photonZfeed/multiDradiometry/CAD/ND-Radiometry-Scanner/leadscrew_support_cap.stl

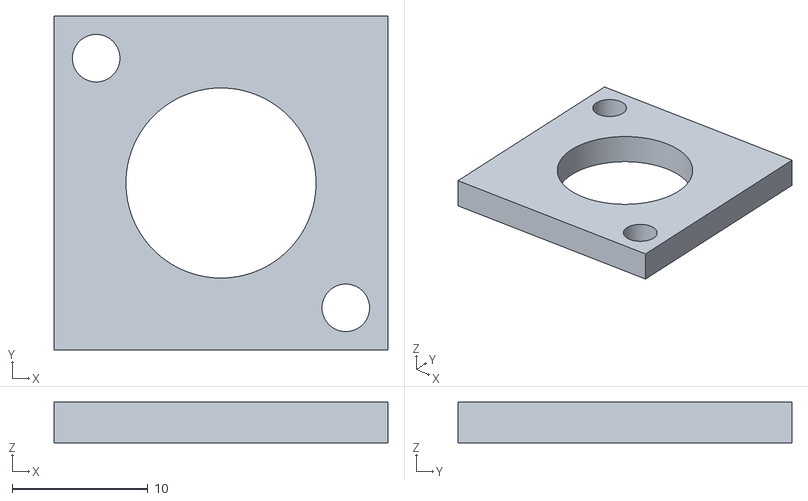
[picture p23: CAD file, 2021-06-03]
CAD/ND-Radiometry-Scanner/leadscrew_support_cap.stl
24.6 x 24.6 x 3.00
