photonZfeed/multiDradiometry/CAD/ND-Radiometry-Scanner/z-sled_nut_cover.stl

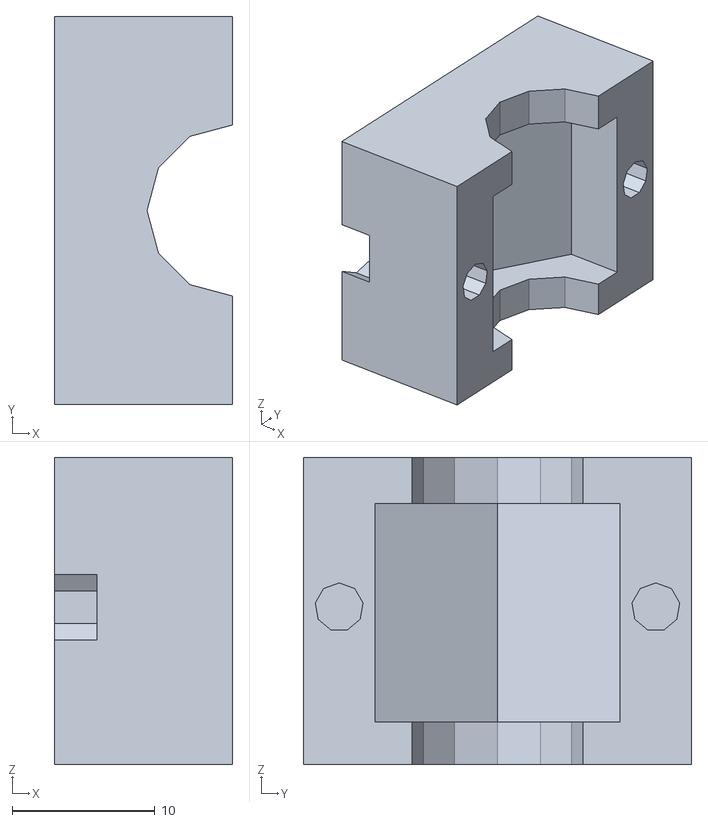
[picture p24: CAD file, 2021-06-03]
CAD/ND-Radiometry-Scanner/z-sled_nut_cover.stl
12.5 x 27.2 x 21.5
