photonZfeed/multiDradiometry/Python/ITOM_script/02Results/210430_115323_example_name/11.58_mm/Colormapexample_name.png

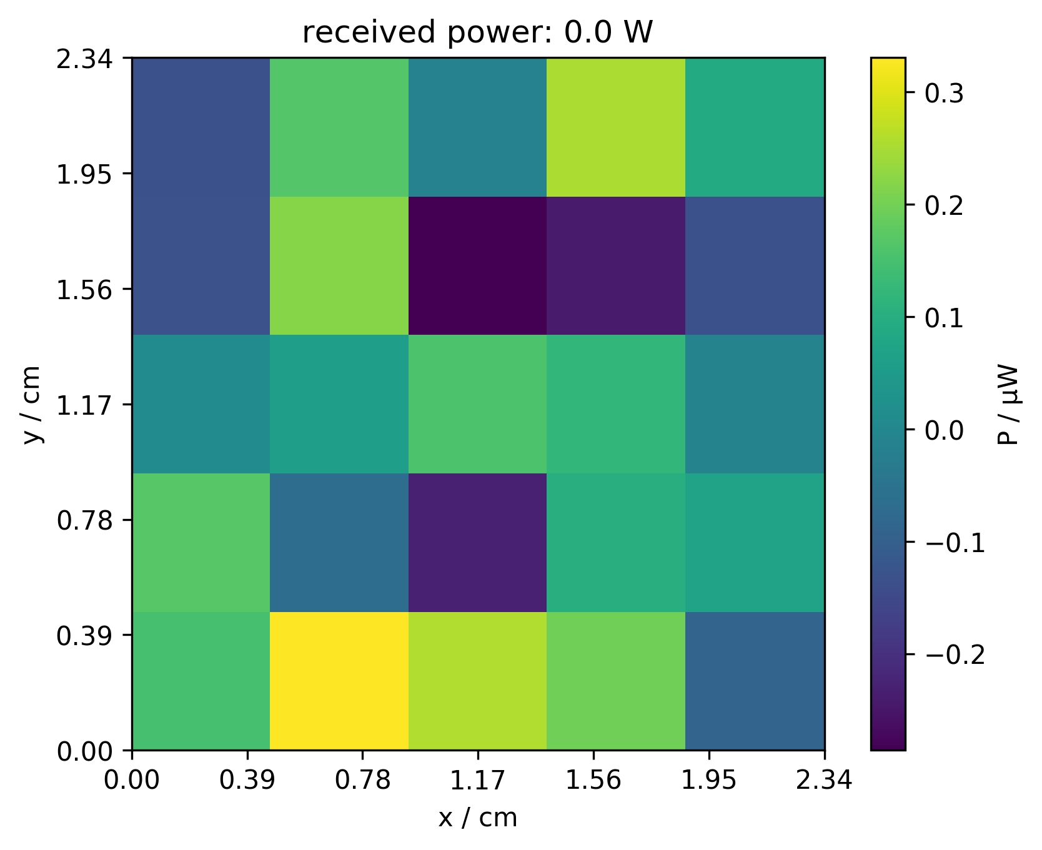
Python/ITOM_script/02Results/210430_115323_example_name/11.58_mm/Colormapexample_name.png
